jasenpashov/volume-nRF52/doc/IMG_20260403_170251.jpg

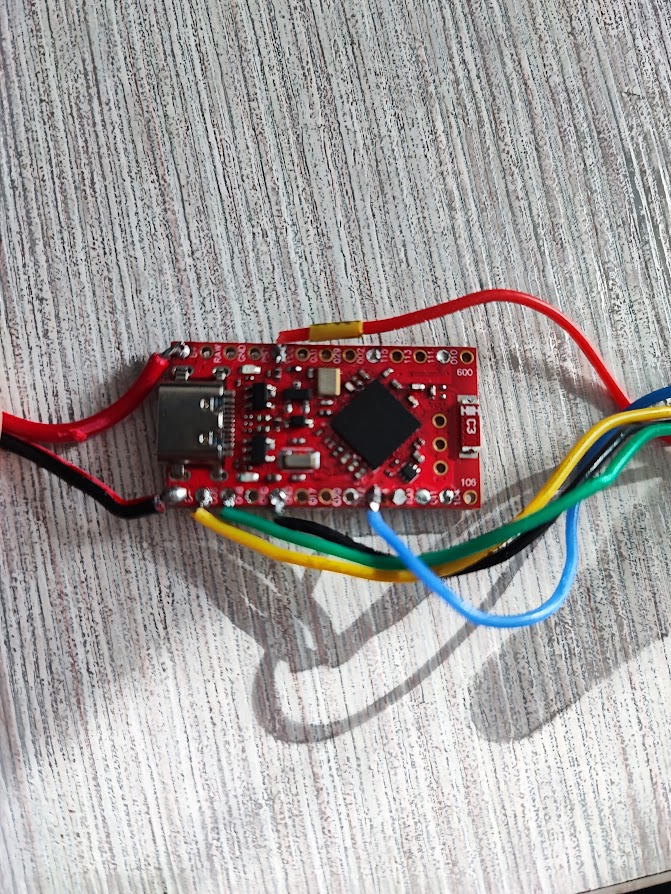
doc/IMG_20260403_170251.jpg
